ddabidov/Headphone-DAC-AMP/image-1.png

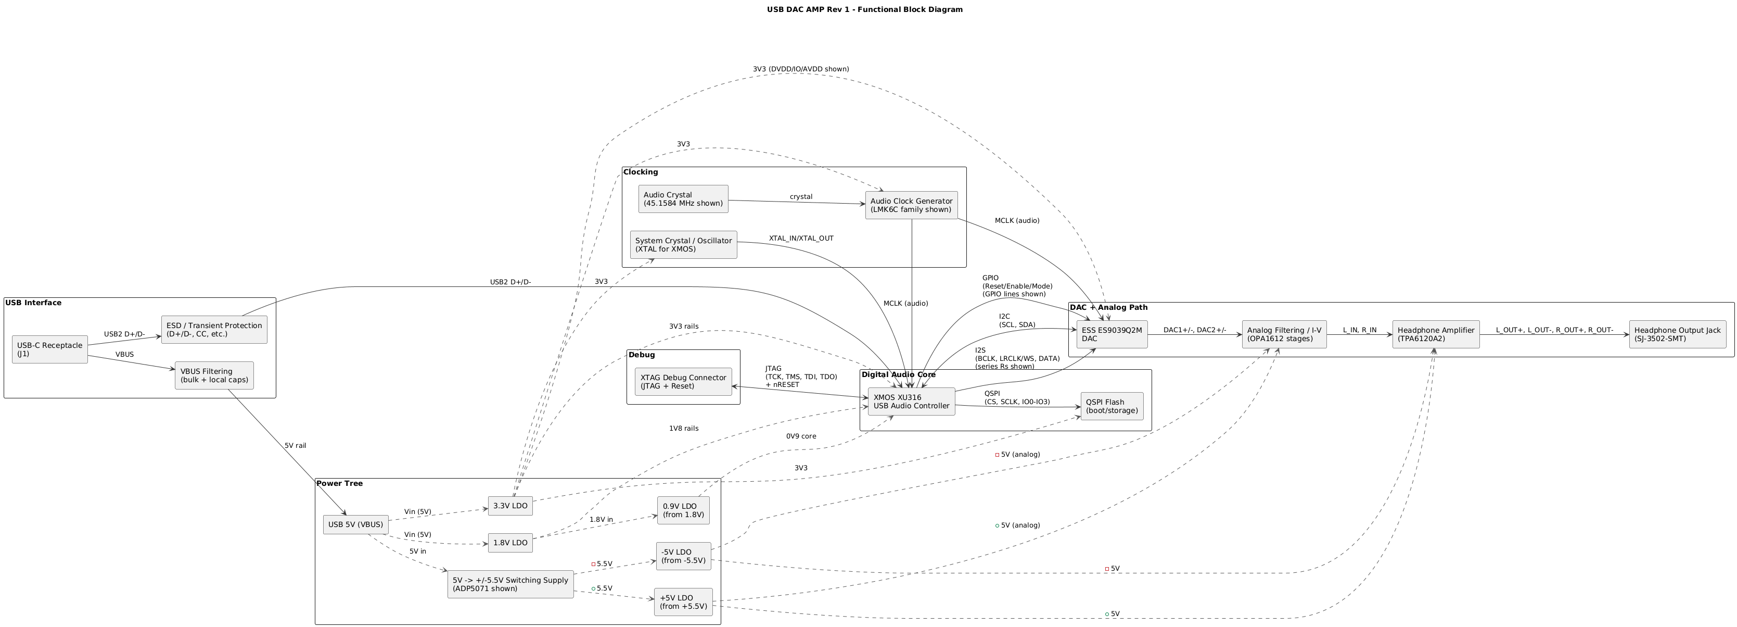
image-1.png
