ddabidov/Headphone-DAC-AMP/image-3.png

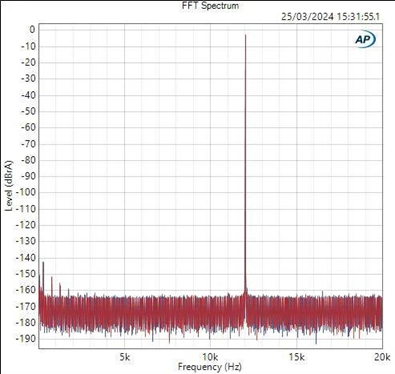
image-3.png
