ddabidov/Headphone-DAC-AMP/image-4.png

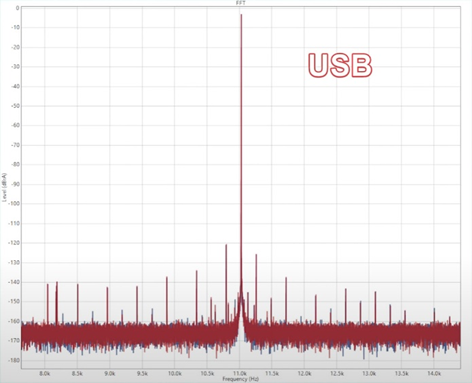
image-4.png
